ziadmohamed0/Takamul_ONA/mechanical/V2/CAD/Back.SLDPRT

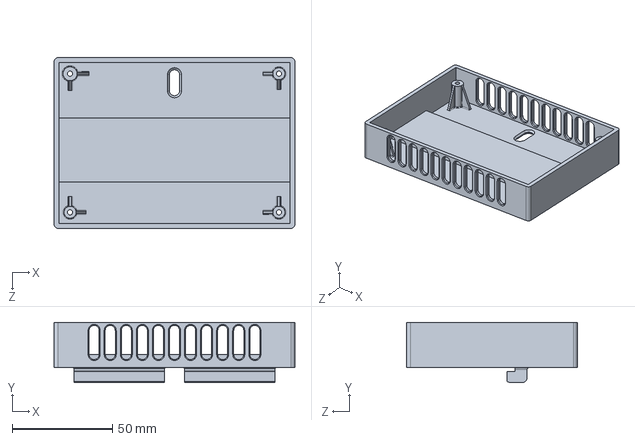
[picture p32: CAD file, 2026-05-09]
mechanical/V2/CAD/Back.SLDPRT
120.0 x 30.0 x 85.0 mm
