ziadmohamed0/Takamul_ONA/mechanical/sample/cad_v2/top_connectors.stl

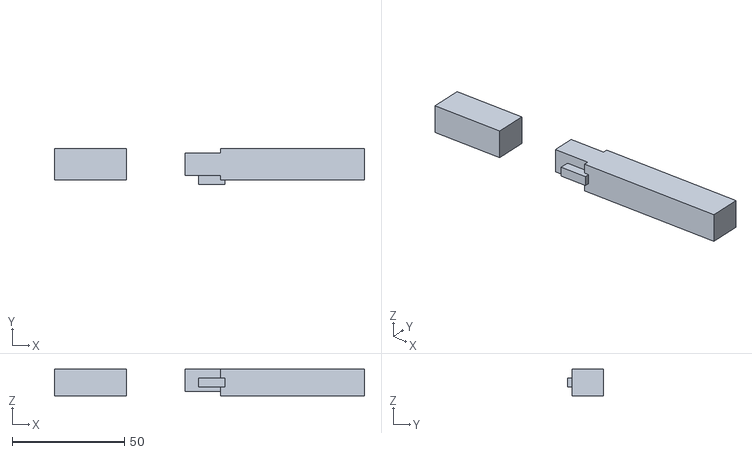
[picture p34: CAD file, 2026-05-02]
mechanical/sample/cad_v2/top_connectors.stl
138.0 x 16.0 x 12.0
