ziadmohamed0/Takamul_ONA/mechanical/V2/CAD/Face.SLDPRT

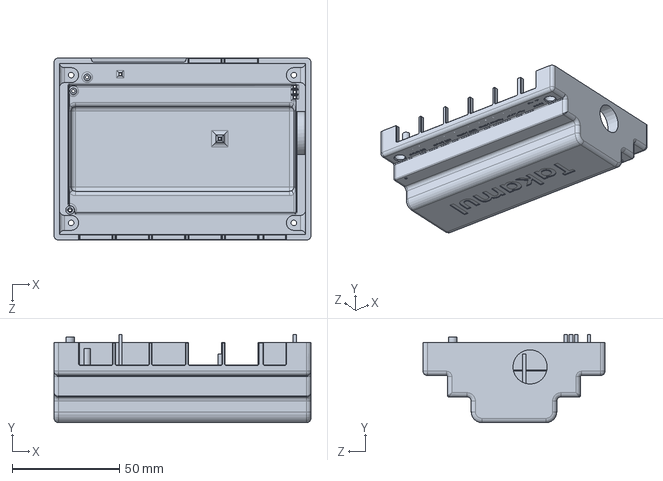
[picture p35: CAD file, 2026-05-09]
mechanical/V2/CAD/Face.SLDPRT
120.0 x 41.2 x 85.0 mm
