ziadmohamed0/Takamul_ONA/mechanical/sample/cad_v2/base.stl

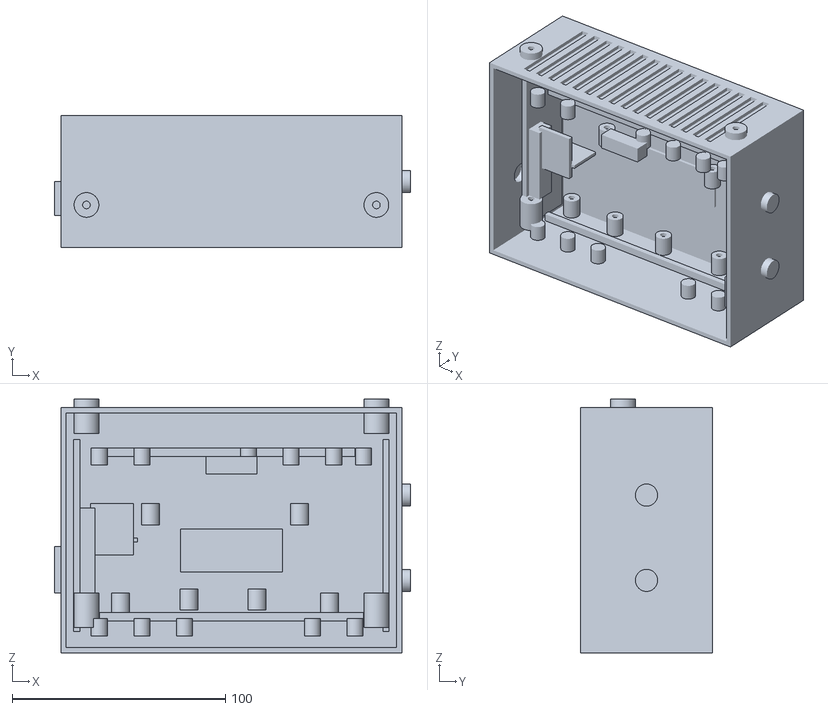
[picture p37: CAD file, 2026-05-02]
mechanical/sample/cad_v2/base.stl
167.0 x 62.0 x 119.0
