ziadmohamed0/Takamul_ONA/ONA_HARD/3d models/kf2edgk-pluggable-terminal-block-1.snapshot.1/STEP/8P.STEP

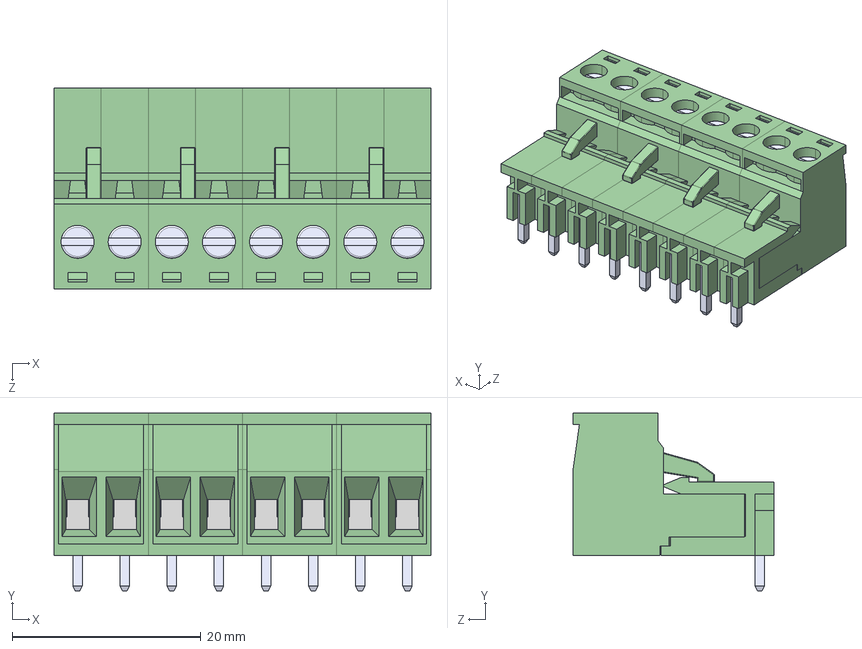
[picture p38: CAD file, 2026-05-02]
ONA_HARD/3d models/kf2edgk-pluggable-terminal-block-1.snapshot.1/STEP/8P.STEP
40.0 x 18.9 x 21.3 mm
6913527100xx_PIN.stp x 8
6913527100xxCAGE.stp x 8
6913527100xx_VIS.stp x 8
691352710002.stp x 4
691352710002_COFFRE.stp x 4
Metal x 8
Socket x 8
