ziadmohamed0/Takamul_ONA/ONA_HARD/3d models/kf2edgk-pluggable-terminal-block-1.snapshot.1/STEP/12P.STEP

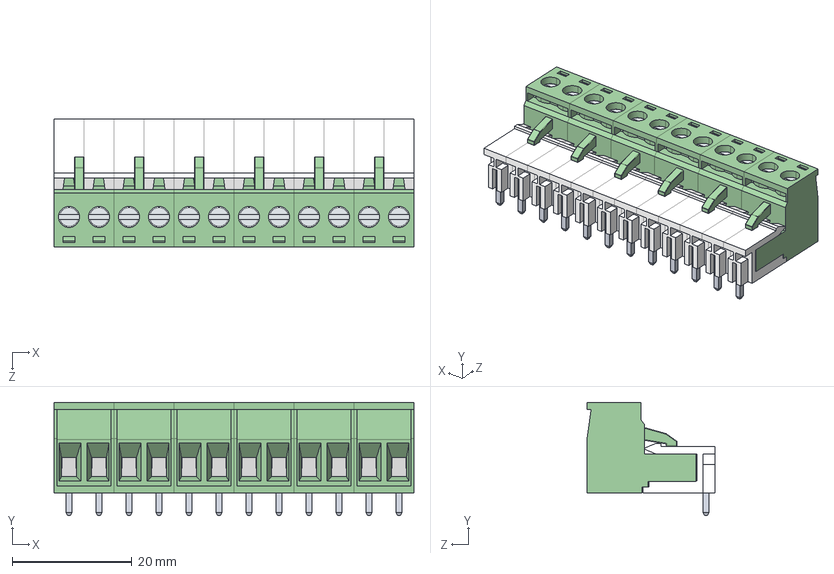
[picture p39: CAD file, 2026-05-02]
ONA_HARD/3d models/kf2edgk-pluggable-terminal-block-1.snapshot.1/STEP/12P.STEP
60.0 x 18.9 x 21.3 mm
6913527100xx_PIN.stp x 12
6913527100xxCAGE.stp x 12
6913527100xx_VIS.stp x 12
691352710002.stp x 6
691352710002_COFFRE.stp x 6
Metal x 12
Socket x 12
