ziadmohamed0/Takamul_ONA/ONA_HARD/3d models/kf2edgk-pluggable-terminal-block-1.snapshot.1/STEP/10P.STEP

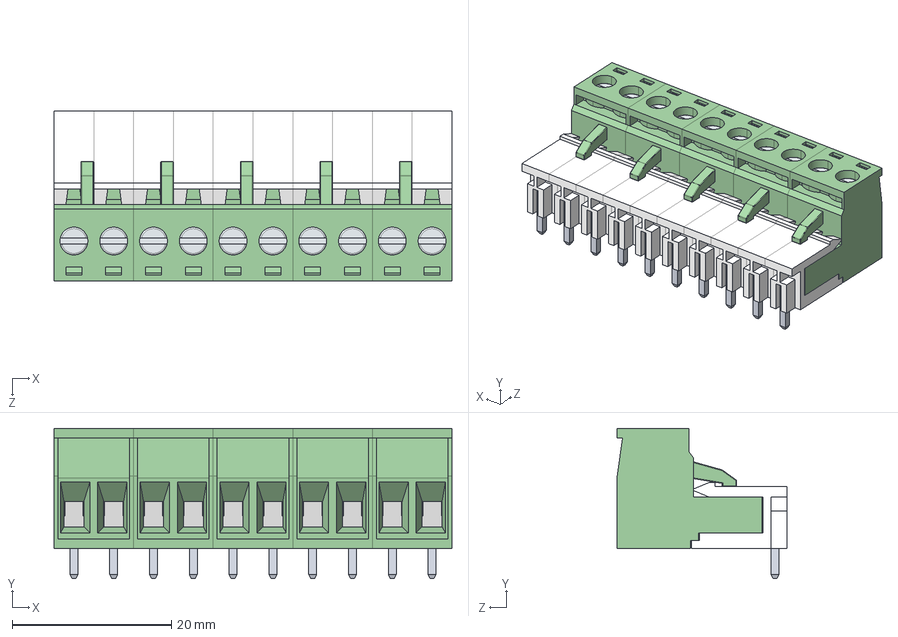
[picture p40: CAD file, 2026-05-02]
ONA_HARD/3d models/kf2edgk-pluggable-terminal-block-1.snapshot.1/STEP/10P.STEP
50.0 x 18.9 x 21.3 mm
6913527100xx_PIN.stp x 10
6913527100xxCAGE.stp x 10
6913527100xx_VIS.stp x 10
691352710002.stp x 5
691352710002_COFFRE.stp x 5
Metal x 10
Socket x 10
