ziadmohamed0/Takamul_ONA/mechanical/sample/cad_v2/bottom_connectors.stl

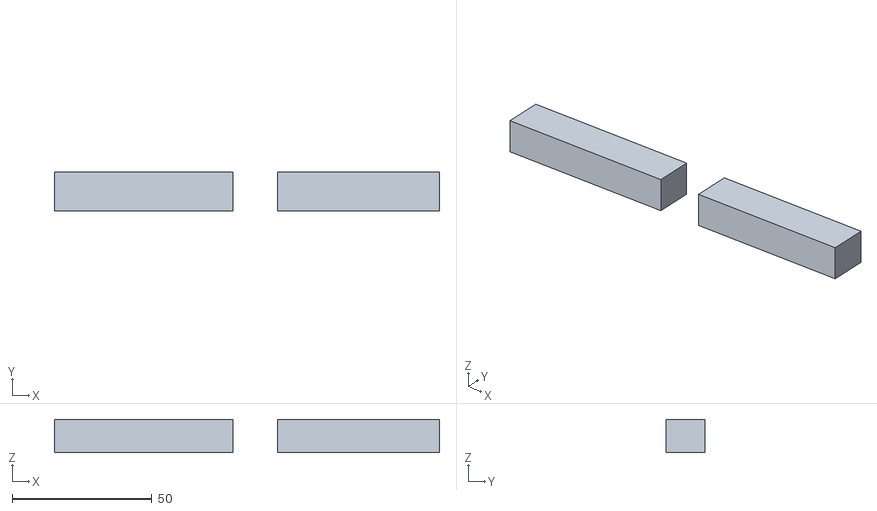
[picture p41: CAD file, 2026-05-02]
mechanical/sample/cad_v2/bottom_connectors.stl
138.0 x 14.0 x 12.0
