ziadmohamed0/Takamul_ONA/ONA_HARD/3d models/kf2edgk-pluggable-terminal-block-1.snapshot.1/STEP/11P.STEP

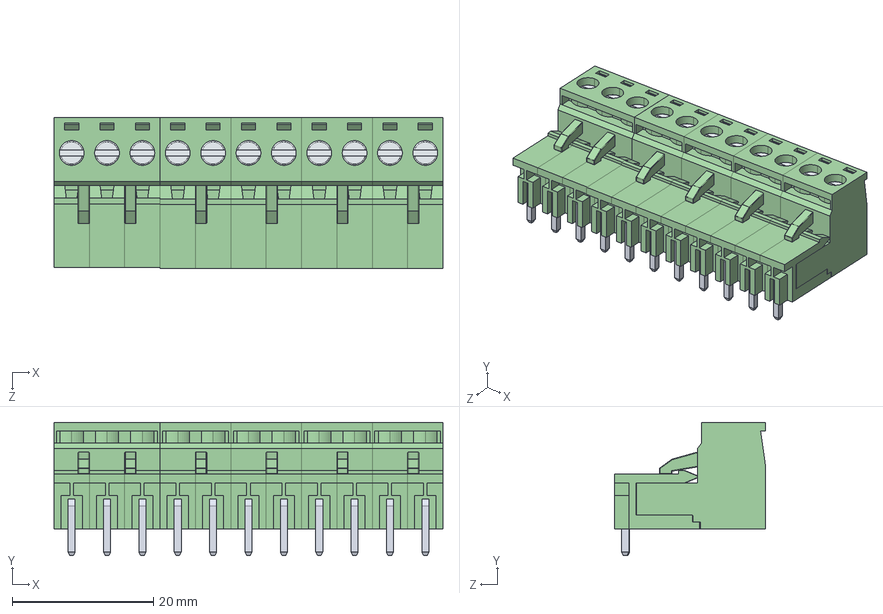
[picture p42: CAD file, 2026-05-02]
ONA_HARD/3d models/kf2edgk-pluggable-terminal-block-1.snapshot.1/STEP/11P.STEP
55.0 x 18.8 x 21.3 mm
6913527100xx_PIN.stp x 11
6913527100xxCAGE.stp x 11
6913527100xx_VIS.stp x 11
691352710003.stp
691352710003_COFFRE.stp
Metal x 11
Socket x 11
691352710002.stp x 4
691352710002_COFFRE.stp x 4
