ziadmohamed0/Takamul_ONA/ONA_HARD/3d models/kf2edgk-pluggable-terminal-block-1.snapshot.1/STEP/6P.STEP

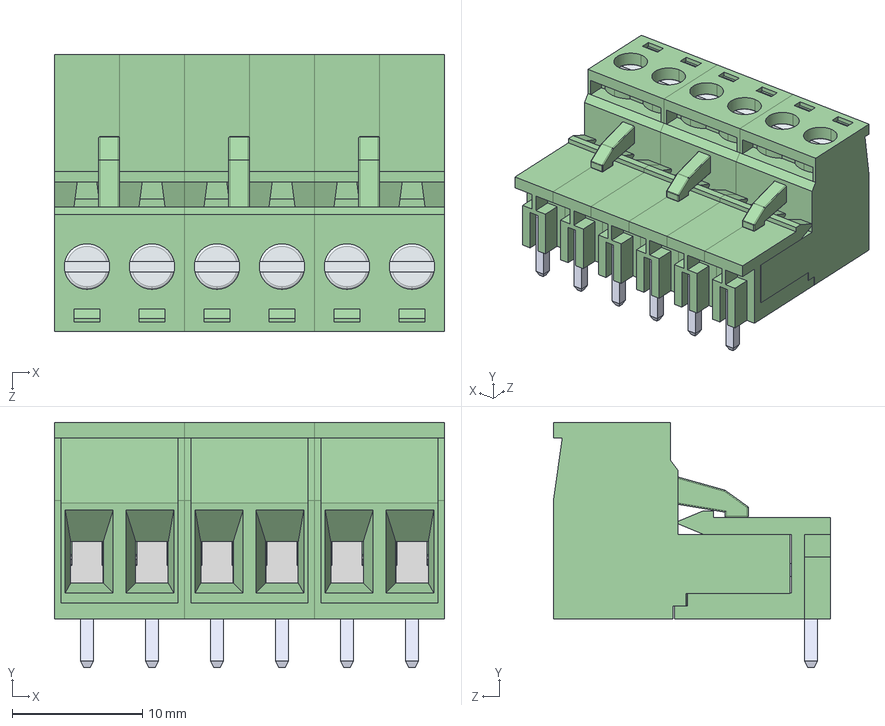
[picture p43: CAD file, 2026-05-02]
ONA_HARD/3d models/kf2edgk-pluggable-terminal-block-1.snapshot.1/STEP/6P.STEP
30.0 x 18.9 x 21.3 mm
6913527100xx_PIN.stp x 6
6913527100xxCAGE.stp x 6
6913527100xx_VIS.stp x 6
691352710002.stp x 3
691352710002_COFFRE.stp x 3
Metal x 6
Socket x 6
