ziadmohamed0/Takamul_ONA/mechanical/sample/cad_v2/din_clip.stl

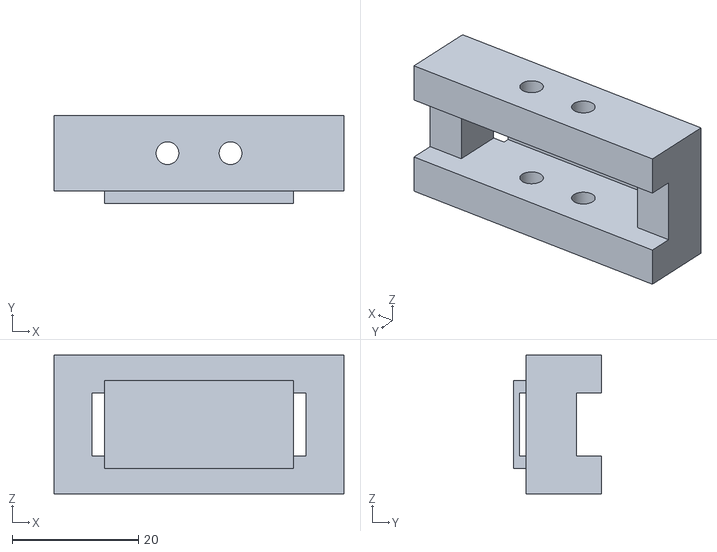
[picture p44: CAD file, 2026-05-02]
mechanical/sample/cad_v2/din_clip.stl
46.0 x 14.0 x 22.0
