ziadmohamed0/Takamul_ONA/ONA_HARD/3d models/kf2edgk-pluggable-terminal-block-1.snapshot.1/STEP/9P.STEP

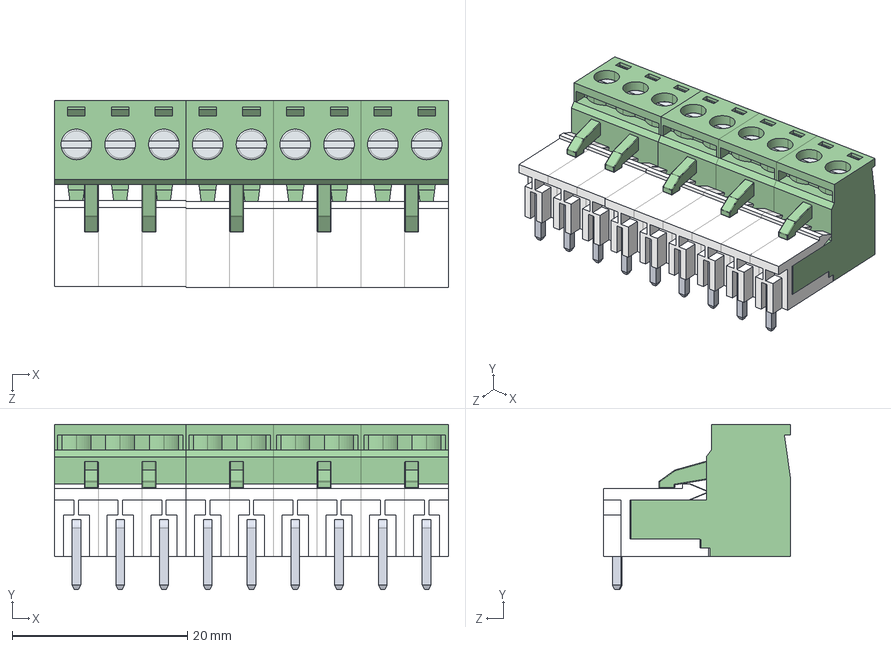
[picture p45: CAD file, 2026-05-02]
ONA_HARD/3d models/kf2edgk-pluggable-terminal-block-1.snapshot.1/STEP/9P.STEP
45.0 x 18.8 x 21.3 mm
6913527100xx_PIN.stp x 9
6913527100xxCAGE.stp x 9
6913527100xx_VIS.stp x 9
691352710003.stp
691352710003_COFFRE.stp
Metal x 9
Socket x 9
691352710002.stp x 3
691352710002_COFFRE.stp x 3
