ziadmohamed0/Takamul_ONA/mechanical/sample/cad_v2/antenna.stl

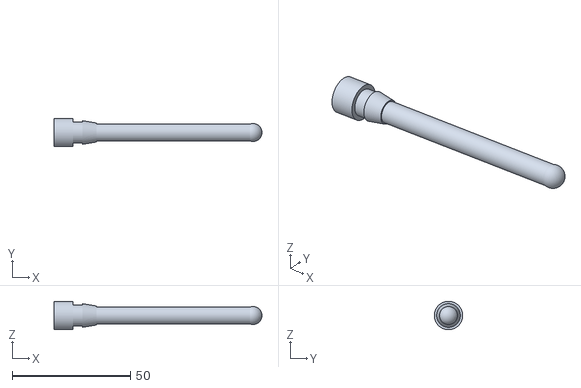
[picture p46: CAD file, 2026-05-02]
mechanical/sample/cad_v2/antenna.stl
87.8 x 12.0 x 12.0
