ziadmohamed0/Takamul_ONA/ONA_HARD/3d models/kf2edgk-pluggable-terminal-block-1.snapshot.1/STEP/2P.STEP

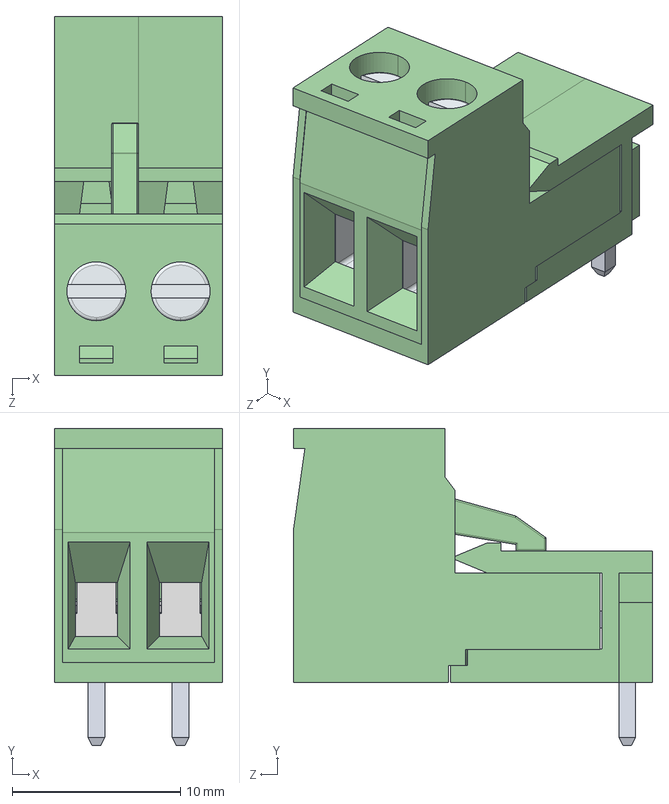
[picture p47: CAD file, 2026-05-02]
ONA_HARD/3d models/kf2edgk-pluggable-terminal-block-1.snapshot.1/STEP/2P.STEP
10.0 x 18.9 x 21.3 mm
6913527100xx_PIN.stp x 2
6913527100xxCAGE.stp x 2
6913527100xx_VIS.stp x 2
691352710002.stp
691352710002_COFFRE.stp
Metal x 2
Socket x 2
