ziadmohamed0/Takamul_ONA/mechanical/sample/cad_v2/standoff.stl

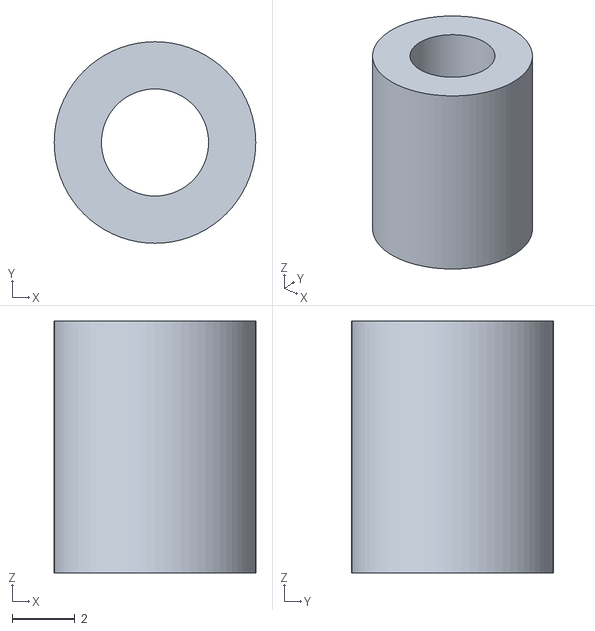
[picture p48: CAD file, 2026-05-02]
mechanical/sample/cad_v2/standoff.stl
6.40 x 6.40 x 8.00
