ziadmohamed0/Takamul_ONA/ONA_Software/tests/modbus_mapping_controll/Core/Inc/main.h

#define DI_Pin GPIO_PIN_2
#define DI_GPIO_Port GPIOA
#define RO_Pin GPIO_PIN_3
#define RO_GPIO_Port GPIOA
#define DE_RE_Pin GPIO_PIN_4
#define DE_RE_GPIO_Port GPIOA
